vladbalmos/746-hfp-conversion/src/pico/audio.c

#include <stdio.h>
#include <stdlib.h>
#include <string.h>
#include "hardware/adc.h"
#include "hardware/clocks.h"
#include "hardware/i2c.h"
#include "hardware/spi.h"
#include "hardware/dma.h"
#include "pico/stdlib.h"
#include "pico/util/queue.h"
#include "pico/multicore.h"
#include "pico/i2c_slave.h"
#include "sample_rate.h"
#include "sine_16000_666.h"
#include "sine_8000_666.h"
#include "audio.h"
#include "debug.h"

// I2C
#define I2C_BAUDRATE 1000000
#define I2C_SDA_PIN 12
#define I2C_SCL_PIN 13
#define I2C_ADDRESS 32

// SPI
#define SPI_BAUDRATE I2C_BAUDRATE
#define SPI_DAC_CS_PIN 17
#define SPI_DAC_SCLK_PIN 18
#define SPI_DAC_TX_PIN 19

#define ADC_CLOCK_SPEED_HZ 48 * 1000 * 1000
#define MAX_BUFFERS 8
#define ADC_SIGNAL_BIAS 2048
#define AUDIO_SINEWAVE_DMA_TIMER 0

#define AUDIO_STATE_NONE 0
#define AUDIO_STATE_INITIALIZED 1

#define CMD_AUDIO_ENABLE 1
#define CMD_AUDIO_RECEIVE 2
#define CMD_AUDIO_POLL 5
#define CMD_AUDIO_TRANSMIT 6
#define CMD_AUDIO_DISABLE 7

#define CMD_REPLY_NONE 0
#define CMD_REPLY_OK 1
#define CMD_REPLY_DATA 7

static int audio_adc_dma_chan;
static int audio_dac_dma_chan;

static sample_rate_t audio_sample_rate;
static uint8_t *adc_samples_buf[MAX_BUFFERS] = {0};
static int8_t adc_samples_buf_index = -1;
static int8_t adc_current_buf_index_streaming = -1;
static uint64_t adc_sampled_count = 0;
static uint64_t adc_streamed_count = 0;

static uint8_t *dac_samples_buf[MAX_BUFFERS] = {0};
static int8_t dac_samples_buf_index = -1;
static int8_t dac_current_buf_index_streaming = -1;
static int8_t dac_streaming = 0;
static uint64_t dac_received_count = 0;
static uint64_t dac_streamed_count = 0;

static size_t buffer_samples_count = 0;
static size_t buffer_size = 0;
static int16_t *sinewave_buf = NULL;
static uint8_t sinewave_enabled = 0;
static queue_t i2c_msg_in_q;
static queue_t i2c_msg_out_q;
static uint8_t initialized = 0;
static uint16_t master_cmd = 0;
static uint8_t current_state = AUDIO_STATE_NONE;
static uint8_t receive_in_progress = 0;
static uint8_t transfer_in_progress = 0;
static size_t bytes_received = 0;
static size_t bytes_sent = 0;
static size_t bytes_available = 0;

#ifdef DEBUG_MODE
static uint64_t sent_adc_counter = 0;
static absolute_time_t adc_start_sampling_us;
static int64_t adc_sampling_duration_us = 0;

static uint64_t sent_dac_counter = 0;
static absolute_time_t dac_start_sampling_us;
static int64_t dac_sampling_duration_us = 0;

static absolute_time_t i2c_receive_audio_start_us;
static int64_t i2c_receive_audio_duration_us;

static absolute_time_t i2c_transfer_audio_start_us;
static int64_t i2c_transfer_audio_duration_us;
#endif

static inline void i2c_read(uint8_t *dst, size_t len) {
    i2c_read_raw_blocking(i2c0, dst, len);
}

static inline void i2c_write(uint8_t *src, size_t len) {
    i2c_write_raw_blocking(i2c0, src, len);
}

static void __isr audio_dac_dma_isr() {
#ifdef DEBUG_MODE
    static absolute_time_t now;

    if (sent_dac_counter) {
        now = get_absolute_time();
        dac_sampling_duration_us = absolute_time_diff_us(dac_start_sampling_us, now);
        dac_start_sampling_us = now;
    }
#endif
    dma_hw->ints1 = 1u << audio_dac_dma_chan;
    
    if (dac_current_buf_index_streaming < 0 || dac_current_buf_index_streaming >= MAX_BUFFERS) {
        dac_current_buf_index_streaming = 0;
    }
    
    dac_streamed_count++;
    dma_channel_set_read_addr(audio_dac_dma_chan, dac_samples_buf[dac_current_buf_index_streaming++], true);
}

static void __isr audio_adc_dma_isr() {
    static int32_t sample;
    static int16_t *buf = NULL;
#ifdef DEBUG_MODE
    static absolute_time_t now;

    if (sent_adc_counter) {
        now = get_absolute_time();
        adc_sampling_duration_us = absolute_time_diff_us(adc_start_sampling_us, now);
        adc_start_sampling_us = now;
    }
#endif
    
    dma_hw->ints0 = 1u << audio_adc_dma_chan;


    if (adc_samples_buf_index != -1) {
        adc_sampled_count++;

        if (!sinewave_enabled) {
            buf = (int16_t *) adc_samples_buf[adc_samples_buf_index - 1];
            for (int i = 0; i < buffer_samples_count; i++) {
                sample = (buf[i] - ADC_SIGNAL_BIAS) * 16;
                if (sample > INT16_MAX) {
                    sample = INT16_MAX;
                } else if (sample < INT16_MIN) {
                    sample = INT16_MIN;
                }
                buf[i] = (int16_t) sample;
            }
        }

    }

    if (adc_samples_buf_index < 0 || adc_samples_buf_index >= MAX_BUFFERS) {
        adc_samples_buf_index = 0;
    }
    if (sinewave_enabled) {
        dma_channel_set_read_addr(audio_adc_dma_chan, sinewave_buf, false);
    }
    dma_channel_set_write_addr(audio_adc_dma_chan, adc_samples_buf[adc_samples_buf_index++], true);
}

// Our handler is called from the I2C ISR, so it must complete quickly. Blocking calls /
// printing to stdio may interfere with interrupt handling.
static void __isr i2c_slave_handler(i2c_inst_t *i2c, i2c_slave_event_t event) {
    static uint16_t cmd_reply = CMD_REPLY_NONE;
    static uint16_t cmd_none_reply = CMD_REPLY_NONE;
    static uint8_t cmd = 0;

    switch (event) {
        case I2C_SLAVE_RECEIVE: {
                                    
            if (!receive_in_progress) {
                i2c_read((uint8_t *) &master_cmd, sizeof(uint16_t));
                cmd = master_cmd >> 8;
            } else {
                cmd = CMD_AUDIO_RECEIVE;
            }

            if (current_state == AUDIO_STATE_NONE) {

                if (cmd == CMD_AUDIO_ENABLE) {
                    queue_try_add(&i2c_msg_in_q, &master_cmd);
                    cmd_reply = CMD_REPLY_OK;
                    queue_try_add(&i2c_msg_out_q, &cmd_reply);
                    cmd_reply = CMD_REPLY_NONE;
                    current_state = AUDIO_STATE_INITIALIZED;
                    break;
                } 

            } else if (current_state == AUDIO_STATE_INITIALIZED) {

                if (cmd == CMD_AUDIO_DISABLE) {
                    queue_try_add(&i2c_msg_in_q, &master_cmd);
                    cmd_reply = CMD_REPLY_OK;
                    queue_try_add(&i2c_msg_out_q, &cmd_reply);
                    cmd_reply = CMD_REPLY_NONE;
                    current_state = AUDIO_STATE_NONE;
                    break;
                }
                
                if (cmd == CMD_AUDIO_POLL) {
                    cmd_reply = (adc_sampled_count > adc_streamed_count) ? CMD_REPLY_OK : CMD_REPLY_NONE;
                    queue_try_add(&i2c_msg_out_q, &cmd_reply);
                    cmd_reply = CMD_REPLY_NONE;
                    break;
                }
                
                if (cmd == CMD_AUDIO_RECEIVE) {
                    if (!receive_in_progress) {
#ifdef DEBUG_MODE
                        i2c_receive_audio_start_us = get_absolute_time();
#endif
                        receive_in_progress = 1;
                        if (dac_samples_buf_index < 0 || dac_samples_buf_index >= MAX_BUFFERS) {
                            dac_samples_buf_index = 0;
                        }
                    }
                    
                    bytes_available = i2c_get_read_available(i2c0);
                    if (!bytes_available) {
                        break;
                    }
                    i2c_read(dac_samples_buf[dac_samples_buf_index] + bytes_received, bytes_available);
                    bytes_received += bytes_available;

                    if (bytes_received == buffer_size) {
#ifdef DEBUG_MODE
                        i2c_receive_audio_duration_us = absolute_time_diff_us(i2c_receive_audio_start_us, get_absolute_time());
#endif
                        receive_in_progress = 0;
                        bytes_received = 0;
                        dac_samples_buf_index++;
                        dac_received_count++;
                        uint16_t master_cmd = cmd << 8;
                        queue_try_add(&i2c_msg_in_q, &master_cmd);
                    }
                    break;
                }
                
                if (cmd == CMD_AUDIO_TRANSMIT) {
                    if (adc_sampled_count >= 3) {
                        cmd_reply = CMD_REPLY_DATA;
                        queue_try_add(&i2c_msg_in_q, &master_cmd);
                    } else {
                        cmd_reply = CMD_REPLY_NONE;
                    }
                    // cmd_reply = CMD_REPLY_DATA;
                    // queue_try_add(&i2c_msg_in_q, &master_cmd);
                    queue_try_add(&i2c_msg_out_q, &cmd_reply);
                    cmd_reply = CMD_REPLY_NONE;
                    break;
                }
            }

            cmd_reply = CMD_REPLY_NONE;
            queue_try_add(&i2c_msg_out_q, &cmd_reply);
            break;
        }
        case I2C_SLAVE_REQUEST: {
            if (!transfer_in_progress) {
                if (!queue_try_remove(&i2c_msg_out_q, &cmd_reply)) {
                    goto empty_reply;
                }
            } else {
                cmd_reply = CMD_REPLY_DATA;
            }
            
            if (cmd_reply == CMD_REPLY_OK) {
                i2c_write((uint8_t *) &cmd_reply, 2);
            } else if (cmd_reply == CMD_REPLY_DATA) {
                if (!transfer_in_progress) {
                    transfer_in_progress = 1;

#ifdef DEBUG_MODE
                    i2c_transfer_audio_start_us = get_absolute_time();
#endif
                    
                    if (adc_current_buf_index_streaming < 0 || adc_current_buf_index_streaming >= MAX_BUFFERS) {
                        adc_current_buf_index_streaming = 0;
                    }
                    adc_streamed_count++;
                }

                bytes_available = i2c_get_write_available(i2c0);
                if (!bytes_available) {
                    break;
                }
                bytes_available = (buffer_size - bytes_sent) > bytes_available ? bytes_available : (buffer_size - bytes_sent);
                i2c_write(adc_samples_buf[adc_current_buf_index_streaming] + bytes_sent, bytes_available);
                bytes_sent += bytes_available;
                
                if (bytes_sent == buffer_size) {
#ifdef DEBUG_MODE
                    i2c_transfer_audio_duration_us = absolute_time_diff_us(i2c_transfer_audio_start_us, get_absolute_time());
#endif
                    transfer_in_progress = 0;
                    bytes_sent = 0;
                    adc_current_buf_index_streaming++;
                }
            } else {
                goto empty_reply;
            }
            
            cmd_reply = 0;
            break;

empty_reply:
            i2c_write((uint8_t *) &cmd_none_reply, 2);
            break;
        }

        default:
            break;
    }
}

void audio_process_master_cmd() {
    uint16_t master_cmd = 0;
    queue_remove_blocking(&i2c_msg_in_q, &master_cmd);
    
    uint8_t cmd = master_cmd >> 8;
    
    if ((cmd == CMD_AUDIO_ENABLE) && !initialized) {
        audio_init((sample_rate_t) (master_cmd & 0xff));
        return;
    }

    if ((cmd == CMD_AUDIO_DISABLE) && initialized) {
        audio_deinit();
        return;
    }
    
    if (cmd == CMD_AUDIO_RECEIVE) {
        if (!dac_streaming && dac_samples_buf_index >= 3) {
            dac_streaming = 1;
            audio_dac_dma_isr();
        }
#ifdef DEBUG_MODE
        if (sent_dac_counter++ % 500 == 0 && dac_current_buf_index_streaming > -1) {
            DEBUG("DAC Data transfered. Sampling duration: %lld us. Receive duration: %lld\n", dac_sampling_duration_us, i2c_receive_audio_duration_us);
        }
#endif
        return;
    }
    
    if (cmd == CMD_AUDIO_TRANSMIT) {
#ifdef DEBUG_MODE
        if (sent_adc_counter++ % 500 == 0 && adc_samples_buf_index > -1) {
            DEBUG("ADC Data transfered. Sampling duration: %lld us. Transfer duration: %lld\n", adc_sampling_duration_us, i2c_transfer_audio_duration_us);
        }
#endif
        return;
    }
}

void audio_transport_init() {
    DEBUG("Initializing audio transport\n");

    queue_init(&i2c_msg_in_q, sizeof(uint16_t), 8);
    queue_init(&i2c_msg_out_q, sizeof(uint16_t), 8);


    // I2C
    gpio_init(I2C_SDA_PIN);
    gpio_set_function(I2C_SDA_PIN, GPIO_FUNC_I2C);
    gpio_pull_up(I2C_SDA_PIN);

    gpio_init(I2C_SCL_PIN);
    gpio_set_function(I2C_SCL_PIN, GPIO_FUNC_I2C);
    gpio_pull_up(I2C_SCL_PIN);
    
    i2c_init(i2c0, I2C_BAUDRATE);
    i2c_slave_init(i2c0, I2C_ADDRESS, i2c_slave_handler);
    DEBUG("Initialized I2C\n");

    // SPI
    spi_init(spi0, SPI_BAUDRATE);
    spi_set_format(spi0, 16, 0, 0, SPI_MSB_FIRST);
    
    gpio_set_function(SPI_DAC_TX_PIN, GPIO_FUNC_SPI);
    gpio_set_function(SPI_DAC_SCLK_PIN, GPIO_FUNC_SPI);
    gpio_set_function(SPI_DAC_CS_PIN, GPIO_FUNC_SPI);

    // Silence please
    gpio_put(SPI_DAC_CS_PIN, 1);
    DEBUG("Initialized SPI\n");
    
}

static void init_audio_sine_dma() {
    sinewave_enabled = 1;
    // Configure sinewave transfer DMA channel
    audio_adc_dma_chan = dma_claim_unused_channel(true);
    assert(audio_adc_dma_chan != -1);
    dma_timer_claim(AUDIO_SINEWAVE_DMA_TIMER);
    
    dma_channel_config cfg = dma_channel_get_default_config(audio_adc_dma_chan);
    channel_config_set_transfer_data_size(&cfg, DMA_SIZE_16);
    channel_config_set_read_increment(&cfg, true);
    channel_config_set_write_increment(&cfg, true);
    channel_config_set_dreq(&cfg, dma_get_timer_dreq(AUDIO_SINEWAVE_DMA_TIMER));

    uint16_t dma_timer_num;
    uint16_t dma_timer_denom;

    if (audio_sample_rate == SAMPLE_RATE_16KHZ) {
        dma_timer_num = 8;
        dma_timer_denom = 62500;
    } else if (audio_sample_rate == SAMPLE_RATE_8KHZ) {
        dma_timer_num = 4;
        dma_timer_denom = 62500;
    }
 

#ifdef DEBUG_MODE
    uint32_t cpu_clock_freq_hz = clock_get_hz(clk_sys);
    float actual_sample_rate = cpu_clock_freq_hz * dma_timer_num / dma_timer_denom;
    DEBUG("Transfering data at %f hz %d %d %d %d\n", actual_sample_rate, cpu_clock_freq_hz, dma_timer_num, dma_timer_denom, audio_sample_rate);
#endif

    dma_timer_set_fraction(AUDIO_SINEWAVE_DMA_TIMER, dma_timer_num, dma_timer_denom);
    
    dma_channel_configure(
        audio_adc_dma_chan,
        &cfg,
        NULL,
        NULL,
        buffer_samples_count,
        false
    );

    dma_channel_set_irq0_enabled(audio_adc_dma_chan, true);
    irq_set_exclusive_handler(DMA_IRQ_0, audio_adc_dma_isr);
    irq_set_enabled(DMA_IRQ_0, true);

    DEBUG("Initialized sine wave\n");
}

static void init_audio_adc_dma() {
    adc_init();

    // Configure ADC DMA channel for sampling the audio signal
    audio_adc_dma_chan = dma_claim_unused_channel(true);
    assert(audio_adc_dma_chan != -1);
    
    dma_channel_config cfg = dma_channel_get_default_config(audio_adc_dma_chan);
    channel_config_set_transfer_data_size(&cfg, DMA_SIZE_16);
    channel_config_set_read_increment(&cfg, false);
    channel_config_set_write_increment(&cfg, true);
    channel_config_set_dreq(&cfg, DREQ_ADC);

    uint16_t clock_div;
    if (audio_sample_rate == SAMPLE_RATE_16KHZ) {
        clock_div = 16 * 1000;
    } else if (audio_sample_rate == SAMPLE_RATE_8KHZ) {
        clock_div = 8 * 1000;
    }
    float adc_clock_div = ADC_CLOCK_SPEED_HZ / clock_div;
    DEBUG("Transfering data at %f hz. Requested sample rate: %d\n", ADC_CLOCK_SPEED_HZ / adc_clock_div, audio_sample_rate);

    adc_gpio_init(26);
    adc_select_input(0);
    adc_fifo_setup(
        true,
        true,
        1,
        false,
        false
    );
    adc_set_clkdiv(adc_clock_div);
    
    dma_channel_configure(
        audio_adc_dma_chan,
        &cfg,
        NULL,
        &adc_hw->fifo,
        buffer_samples_count,
        false
    );

    dma_channel_set_irq0_enabled(audio_adc_dma_chan, true);
    irq_set_exclusive_handler(DMA_IRQ_0, audio_adc_dma_isr);
    irq_set_enabled(DMA_IRQ_0, true);
    DEBUG("Initialized ADC\n");
}

static void init_audio_dac_dma() {
    audio_dac_dma_chan = dma_claim_unused_channel(true);

    dma_channel_config cfg = dma_channel_get_default_config(audio_dac_dma_chan);

    channel_config_set_transfer_data_size(&cfg, DMA_SIZE_16);
    channel_config_set_read_increment(&cfg, true);
    channel_config_set_write_increment(&cfg, false);

    if (sinewave_enabled) {
        channel_config_set_dreq(&cfg, dma_get_timer_dreq(AUDIO_SINEWAVE_DMA_TIMER));
    } else {
        channel_config_set_dreq(&cfg, DREQ_ADC);
    }
    
    dma_channel_configure(
        audio_dac_dma_chan,
        &cfg,
        &spi_get_hw(spi0)->dr,
        NULL,
        buffer_samples_count,
        false
    );

    dma_channel_set_irq1_enabled(audio_dac_dma_chan, true);
    irq_set_exclusive_handler(DMA_IRQ_1, audio_dac_dma_isr);
    irq_set_enabled(DMA_IRQ_1, true);

    gpio_put(SPI_DAC_CS_PIN, 0);
    DEBUG("Initialized DAC\n");
}

void audio_init(sample_rate_t sample_rate) {
    DEBUG("Initializing ADC\n");

    DEBUG("Sample rate raw value: %d\n", sample_rate);
    assert(sample_rate == SAMPLE_RATE_16KHZ || sample_rate == SAMPLE_RATE_8KHZ);
    
    if (sample_rate == SAMPLE_RATE_8KHZ) {
        buffer_samples_count = 60;
        sinewave_buf = sinewave_8000;
        DEBUG("Sample rate: 8khz\n");
    }
    if (sample_rate == SAMPLE_RATE_16KHZ) {
        buffer_samples_count = 120;
        sinewave_buf = sinewave_16000;
        DEBUG("Sample rate: 16khz\n");
    }
    
    buffer_size = buffer_samples_count * sizeof(uint16_t);
    DEBUG("ADC buffer samples count: %d\n", buffer_samples_count);
    
    audio_sample_rate = sample_rate;

    for (int i = 0; i < MAX_BUFFERS; i++) {
        // ADC buffers
        adc_samples_buf[i] = malloc(buffer_size);
        if (adc_samples_buf[i] == NULL) {
            panic("Unable to allocate memory for ADC buffer\n");
        }
        assert(adc_samples_buf[i] != NULL);
        memset(adc_samples_buf[i], 0, buffer_size);

        // DAC buffers
        dac_samples_buf[i] = malloc(buffer_size);
        if (dac_samples_buf[i] == NULL) {
            panic("Unable to allocate memory for ADC buffer\n");
        }
        assert(dac_samples_buf[i] != NULL);
        memset(dac_samples_buf[i], 0, buffer_size);
    }
    
    init_audio_adc_dma();
    // init_audio_sine_dma();
    init_audio_dac_dma();
    
#ifdef DEBUG_MODE
    adc_start_sampling_us = get_absolute_time();
#endif

    initialized = 1;
    audio_adc_dma_isr();
    if (!sinewave_enabled) {
        adc_run(true);
    }
}

void audio_deinit() {
    DEBUG("De-initializing audio\n");
    
    // De-init ADC DMA
    dma_channel_set_irq0_enabled(audio_adc_dma_chan, false);
    irq_set_enabled(DMA_IRQ_0, false);
    irq_remove_handler(DMA_IRQ_0, audio_adc_dma_isr);
    dma_channel_abort(audio_adc_dma_chan);
    if (!sinewave_enabled) {
        adc_run(false);
        adc_fifo_drain();
        DEBUG("Drained ADC fifo\n");
    }
    dma_channel_unclaim(audio_adc_dma_chan);
    DEBUG("Disabled ADC DMA\n");

    // De-init DAC DMA
    dma_channel_set_irq0_enabled(audio_dac_dma_chan, false);
    irq_set_enabled(DMA_IRQ_1, false);
    irq_remove_handler(DMA_IRQ_1, audio_dac_dma_isr);
    dma_channel_abort(audio_dac_dma_chan);
    dma_channel_unclaim(audio_dac_dma_chan);
    DEBUG("Disabled DAC DMA\n");

    if (dma_timer_is_claimed(AUDIO_SINEWAVE_DMA_TIMER)) {
        dma_timer_unclaim(AUDIO_SINEWAVE_DMA_TIMER);
        DEBUG("Unclaimed sinewave DMA timer\n");
    }
    
    // Free buffers
    for (int i = 0; i < MAX_BUFFERS; i++) {
        free(adc_samples_buf[i]);
        adc_samples_buf[i] = NULL;

        free(dac_samples_buf[i]);
        dac_samples_buf[i] = NULL;
    }
    
    sinewave_buf = NULL;
    DEBUG("Freed buffers\n");

    adc_samples_buf_index = -1;
    adc_current_buf_index_streaming = -1;
    adc_sampled_count = 0;
    adc_streamed_count = 0;

    dac_samples_buf_index = -1;
    dac_current_buf_index_streaming = -1;
    dac_streaming = 0;
    dac_received_count = 0;
    dac_streamed_count = 0;
    
    bytes_received = 0;
    bytes_sent = 0;
    bytes_available = 0;
    
    transfer_in_progress = 0;
    receive_in_progress = 0;
    current_state = AUDIO_STATE_NONE;
    
    master_cmd = 0;

    buffer_samples_count = 0;
    buffer_size = 0;

    audio_sample_rate = SAMPLE_RATE_NONE;
    sinewave_enabled = 0;
    initialized = 0;
    DEBUG("Reset counters and flags\n");

    gpio_put(SPI_DAC_CS_PIN, 1);
    DEBUG("Reset SPI\n");
    
    // Drain I2C fifo
    size_t bytes_to_discard = i2c_get_read_available(i2c0);
    for (int i = 0; i < bytes_to_discard; i++) {
        i2c_read_byte_raw(i2c0);
    }
    DEBUG("Discarded %d bytes of I2C data\n", bytes_to_discard);
}
