vladbalmos/746-hfp-conversion/src/esp32/main/ringer.h

#include <inttypes.h>
#include "driver/gpio.h"

#define RG_TAG "RINGER"

void ringer_init(gpio_num_t enable_pin, gpio_num_t signal_pin);
void ringer_enable(uint8_t status);
uint8_t ringer_get_state();
